ogunasekara/BentoBot/src/firmware/right_wheel_new_test.csv

ang_vel | motor_cmd
-1.7932195121951289 | -255
-1.7999029126213655 | -250
-1.7191219512195155 | -245
-1.6415048543689252 | -240
-1.5693170731707293 | -235
-1.5070873786407761 | -230
-1.4575728155339767 | -225
-1.416926829268292 | -220
-1.3830582524271813 | -215
-1.355560975609757 | -210
-1.3279611650485434 | -205
-1.2952195121951218 | -200
-1.2645145631067933 | -195
-1.2309756097560944 | -190
-1.194514563106794 | -185
-1.1638536585365835 | -180
-1.130533980582523 | -175
-1.0963414634146353 | -170
-1.0579126213592271 | -165
-1.0182038834951457 | -160
-0.9820487804878029 | -155
-0.9385922330097104 | -150
-0.8939024390243874 | -145
-0.8533009708737845 | -140
-0.8078048780487819 | -135
-0.7548543689320386 | -130
-0.7047804878048779 | -125
-0.6530097087378647 | -120
-0.597463414634148 | -115
-0.544563106796118 | -110
-0.4858536585365849 | -105
-0.42414634146341423 | -100
-0.36229268292682926 | -95
-0.3004368932038833 | -90
-0.22965853658536606 | -85
-0.1607766990291258 | -80
-0.07775609756097587 | -75
-0.0035436893203883504 | -70
0.0 | -65
0.0 | -60
0.0 | -55
0.0 | -50
0.0 | -45
0.0 | -40
0.0 | -35
0.0 | -30
0.0 | -25
0.0 | -20
0.0 | -15
0.0 | -10
0.0 | -5
1.750485436893204 | 255
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
