ogunasekara/BentoBot/src/firmware/right_wheel_test.csv

motor_cmd | ang_vel
-255 | -1.6650970873786446
-250 | -1.6769268292682957
-245 | -1.5988292682926823
-240 | -1.529708737864075
-235 | -1.463853658536585
-230 | -1.409951456310679
-225 | -1.3640000000000052
-220 | -1.3233009708737822
-215 | -1.2836585365853663
-210 | -1.251747572815535
-205 | -1.2265533980582506
-200 | -1.1971359223300955
-195 | -1.1668446601941715
-190 | -1.1355609756097527
-185 | -1.1072330097087375
-180 | -1.0759999999999967
-175 | -1.0421844660194164
-170 | -1.0113170731707306
-165 | -0.9765048543689312
-160 | -0.9385922330097106
-155 | -0.8990731707317052
-150 | -0.8595631067961162
-145 | -0.8199512195121941
-140 | -0.7751707317073173
-135 | -0.732087378640776
-130 | -0.6883414634146362
-125 | -0.6380097087378623
-120 | -0.5907317073170736
-115 | -0.5371844660194176
-110 | -0.482487804878048
-105 | -0.42597087378640763
-100 | -0.36458536585365825
-95 | -0.3055825242718437
-90 | -0.23995145631067866
-85 | -0.16770731707317046
-80 | -0.08684466019417476
-75 | -0.004390243902439026
-70 | 0.0
-65 | 0.0
-60 | 0.0
-55 | 0.0
-50 | 0.0
-45 | 0.0
-40 | 0.0
-35 | 0.0
-30 | 0.0
-25 | 0.0
-20 | 0.0
-15 | 0.0
-10 | 0.0
-5 | 0.0
255 | 1.6178155339805858
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
